iorodeo/panels_g4_hardware/docs/assets/shield_comm_v0p1_front.png

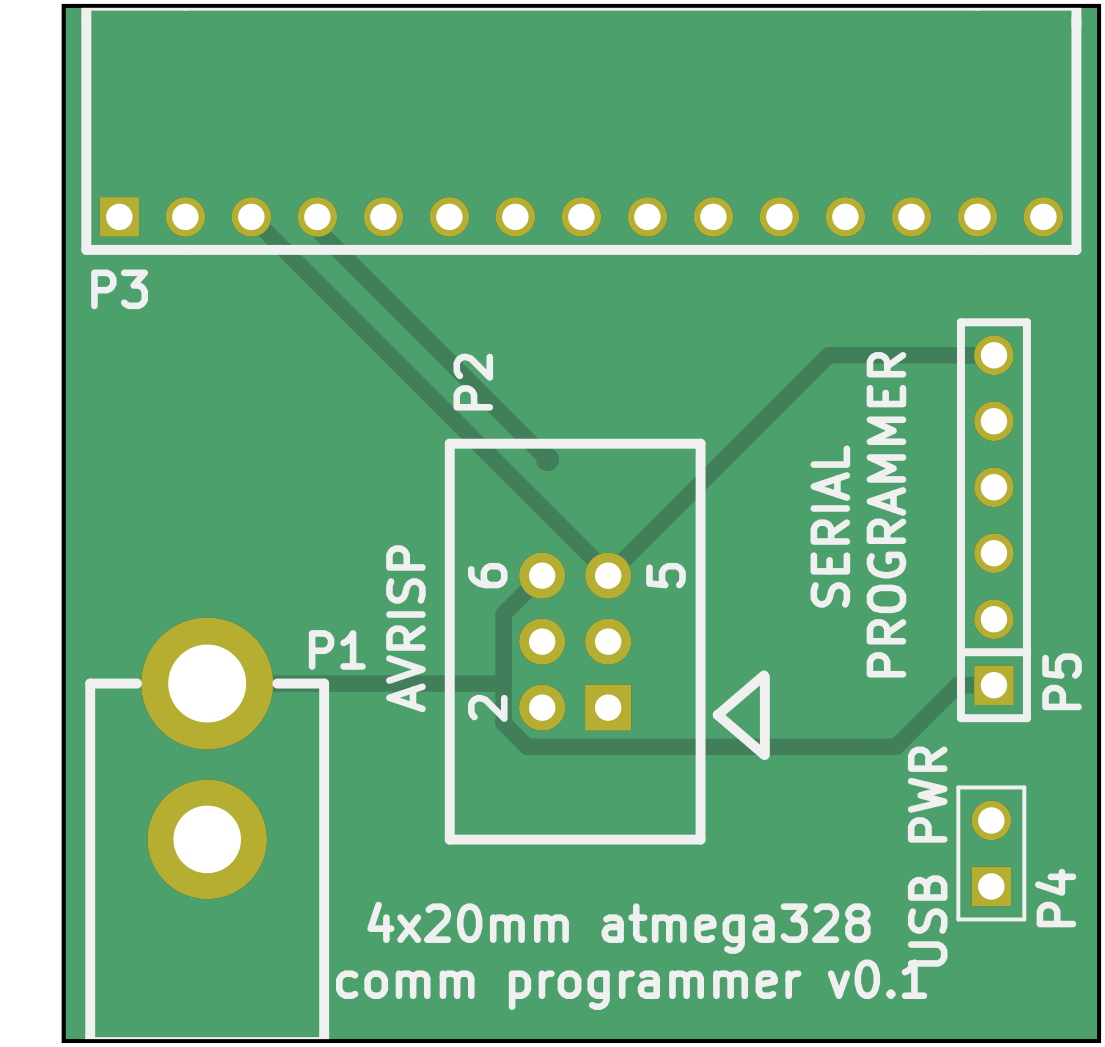
docs/assets/shield_comm_v0p1_front.png
