iorodeo/panels_g4_hardware/docs/assets/shield_driver_v0p1_back.png

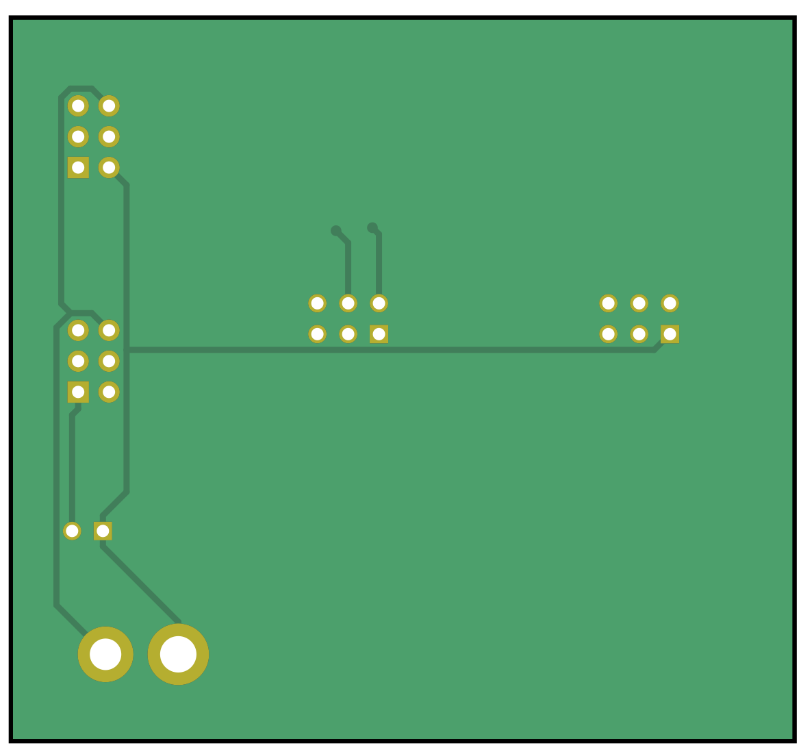
docs/assets/shield_driver_v0p1_back.png
