iorodeo/panels_g4_hardware/docs/assets/shield_driver_v0p1_front.png

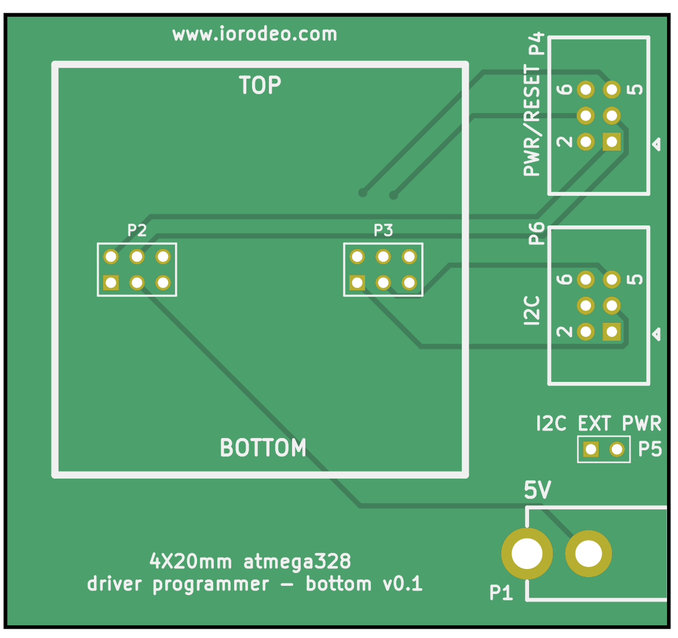
docs/assets/shield_driver_v0p1_front.png
