iorodeo/panels_g4_hardware/docs/assets/shield_programmer_v0p1_back.png

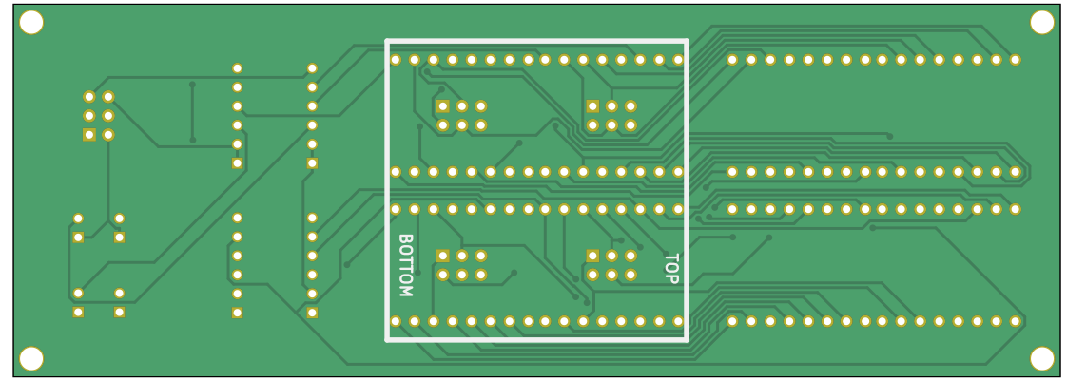
docs/assets/shield_programmer_v0p1_back.png
