iorodeo/panels_g4_hardware/stm32/pcb_big_v1/BOM.xls

Value | Reference | Vendor | Vendor P/N
USB1 | USBSMD | Digikey | 670-1190-1-ND
U1 | UA78M00 | Digikey | 296-12290-1-ND
