iorodeo/panels_g4_hardware/stm32/pcb_big_v1/maple-r5-BOM.xls

Production qty:
Items in red are DNP
Part | Value | Package | Position (inch) | Orientation | Vendor | Vendor P/N
BAR | POWER_JACKPTH | POWER_JACK_PTH | (-0.105 0.5) | R270 | Digikey | CP-002A-ND
BUT |  | PUSHBUTTON-KMR241GLFS | (1.79 1.595) | R180 | Digikey | 401-1426-1-ND
C1 | 33pF | C0402 | (1.08 0.433) | R0 | Digikey | 478-1076-1-ND
C2 | 33pF | C0402 | (1.27 0.31) | R90 | Digikey | 478-1076-1-ND
C3 | 1.0uF | C0402 | (0.06 1.855) | R180 | Digikey | 399-4873-1-ND
C4 | 22uF | UD-4X5,8_NICHICON | (0.89 0.49) | R180 | Digikey | PCE4529CT-ND
C5 | 1.0uF | C0402 | (1.43 0.5) | R180 | Digikey | 399-4873-1-ND
C6 | 1.0uF | C0402 | (1.565 0.935) | R180 | Digikey | 399-4873-1-ND
C7 | 1.0uF | C0402 | (1.068 1.106) | R0 | Digikey | 399-4873-1-ND
C8 | 1.0uF | C0402 | (1.025 0.58) | R90 | Digikey | 399-4873-1-ND
C9 | 47pF | C0402 | (0.432 1.111) | R0 | Digikey | 399-1019-1-ND
C10 | 47pF | C0402 | (0.432 0.961) | R0 | Digikey | 399-1019-1-ND
C11 | 1.0uF | C0402 | (0.5 1.41) | R0 | Digikey | 399-4873-1-ND
C12 | 22uF | UD-4X5,8_NICHICON | (0.65 0.49) | R180 | Digikey | PCE4529CT-ND
C13 | 22uF | UD-4X5,8_NICHICON | (0.89 0.31) | R180 | Digikey | PCE4529CT-ND
D1 | Blue | LED-0603 | (0.6 1.66) | R270 | Digikey | P13484CT-ND
D2 |  | SOD323-W | (0.22 0.72) | R180 | Digikey | 568-4124-1-ND
D3 | Red | LED-0603 | (0.695 1.515) | R90 | Digikey | P11486CT-ND
D4 | Green | LED-0603 | (0.695 1.565) | R90 | Digikey | P11480CT-ND
EXT |  | MA08-2 | (1.9 0.85) | R90 | Digikey | S7111-ND
IC1 | BQ24010DRCA | PSON10-V2 | (0.14 1.755) | R180 | Digikey | 296-13714-1-ND
IC2 | MCP1703T | SOT23 | (0.54 0.31) | R0 | Digikey | MCP1703T-3302E/CBCT-ND
IC3 | MCP1703T | SOT23 | (0.71 0.31) | R0 | Digikey | MCP1703T-3302E/CBCT-ND
J1-A |  | 1X08 | (1.85 2) | R180 | Digikey | S7006-ND
J1-B |  | 1X08-SQUARE | (1.5 1.9) | R180
J2 |  | 1X06 | (1.35 0.1) | R0 | Digikey | S7004-ND
J3-A |  | 1X08 | (0.985 2) | R180 | Digikey | S7006-ND
J3-B |  | 1X08-SQUARE | (0.6 1.9) | R180
J4 | POWER | 1X06 | (0.65 0.1) | R0 | Digikey | S7004-ND
JP1 |  | 1X02 | (0.063 0.45) | R90
JTAG |  | MA04-2 | (0.75 0.8) | R90
LIPO | LiPo | S2B-PH | (0.15 1.5) | R90 | Digikey | 455-1749-1-ND
OSC | 8MHz | CRYSTAL-SMD-5X3 | (1.125 0.338) | R180 | Digikey | 535-9720-1-ND
PWR |  | MA04-2 | (0.65 1.275) | R270 | Digikey | 609-3235-ND
Q2 |  | SOT23 | (0.555 0.92) | R180 | Digikey | BC817K-25E6327INCT-ND
Q3 |  | SOT23 | (0.555 0.76) | R0 | Digikey | BC817K-25E6327INCT-ND
R1 | 1k | C0402 | (0.37 0.18) | R0 | Digikey | P1.0KJCT-ND
R2 | 10k | C0402 | (1.655 1.49) | R90 | Digikey | 311-10KJRCT-ND
R3 | 1k | C0402 | (1.62 1.625) | R0 | Digikey | P1.0KJCT-ND
R4 | 10k | C0402 | (0.545 0.08) | R270 | Digikey | 311-10KJRCT-ND
R5 | 1k | C0402 | (1.285 1.18) | R270 | Digikey | P1.0KJCT-ND
R6 | 1k | C0402 | (0.5 1.66) | R0 | Digikey | P1.0KJCT-ND
R7 | 1.5k | C0402 | (0.432 0.911) | R0 | Digikey | P1.5KJCT-ND
R8 | 36k | C0402 | (0.432 0.861) | R0 | Digikey | 311-36.0KLRCT-ND
R9 | 10k | C0402 | (0.432 0.811) | R180 | Digikey | 311-10KJRCT-ND
R10 | 47k | C0402 | (0.432 0.761) | R180 | Digikey | 311-47.0KLRCT-ND
R12 | 1k | C0402 | (0.432 0.711) | R0 | Digikey | P1.0KJCT-ND
R13 | 22 | C0402 | (0.432 1.061) | R180 | Digikey | 311-22.0LRCT-ND
R14 | 22 | C0402 | (0.432 1.011) | R180 | Digikey | 311-22.0LRCT-ND
R15 | 1.5k | C0402 | (0.432 1.161) | R0 | Digikey | P1.5KJCT-ND
R16 | 1.5k | C0402 | (0.432 1.211) | R180 | Digikey | P1.5KJCT-ND
R18 | 1k | C0402 | (0.155 1.855) | R180 | Digikey | P1.0KJCT-ND
R19 | 1k | C0402 | (0.5 1.56) | R0 | Digikey | P1.0KJCT-ND
R20 | 1k | C0402 | (0.5 1.61) | R0 | Digikey | P1.0KJCT-ND
R22 | 10k | C0402 | (0.5 1.51) | R0 | Digikey | 311-10KJRCT-ND
R23 | 10k | C0402 | (0.5 1.46) | R0 | Digikey | 311-10KJRCT-ND
RESET |  | PUSHBUTTON-KMR241GLFS | (0.4 0.08) | R0 | Digikey | 401-1426-1-ND
RTC |  | 1X02 | (1.75 0.4) | R180
UC1 | STM32F103RBT6 | TQFP-10X10-64 | (1.261 0.783) | R90 | Digikey | 497-6066-ND
X1 | USBSMD | USB-MINIB | (0.2 1.02) | R0 | Digikey | 670-1190-1-ND
